TKJElectronics/BalancingRobot/3D Model/Rendered images/Back top left.jpg

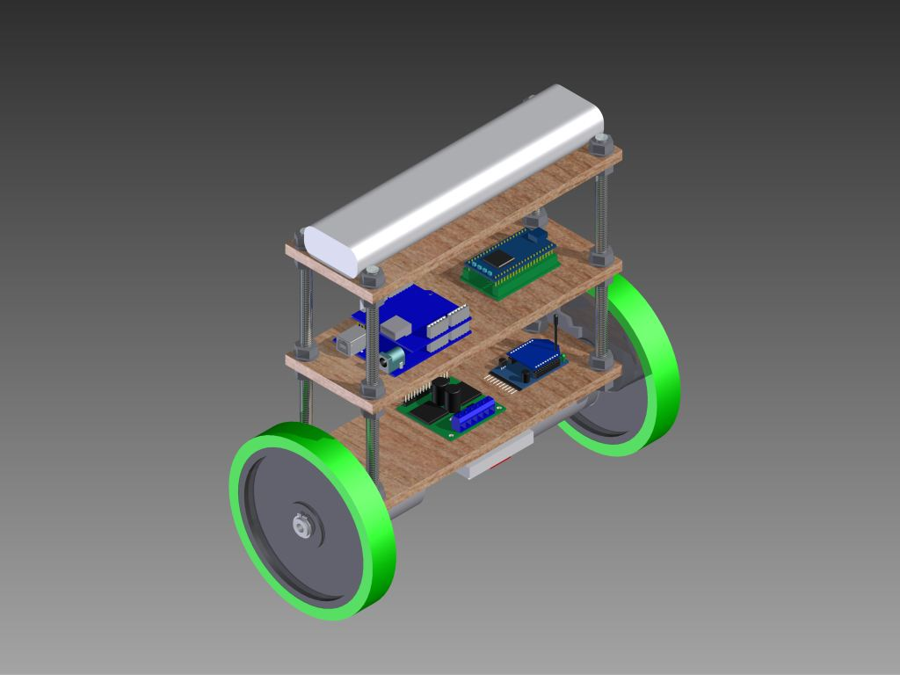
3D Model/Rendered images/Back top left.jpg
