TKJElectronics/BalancingRobot/3D Model/Rendered images/Front.jpg

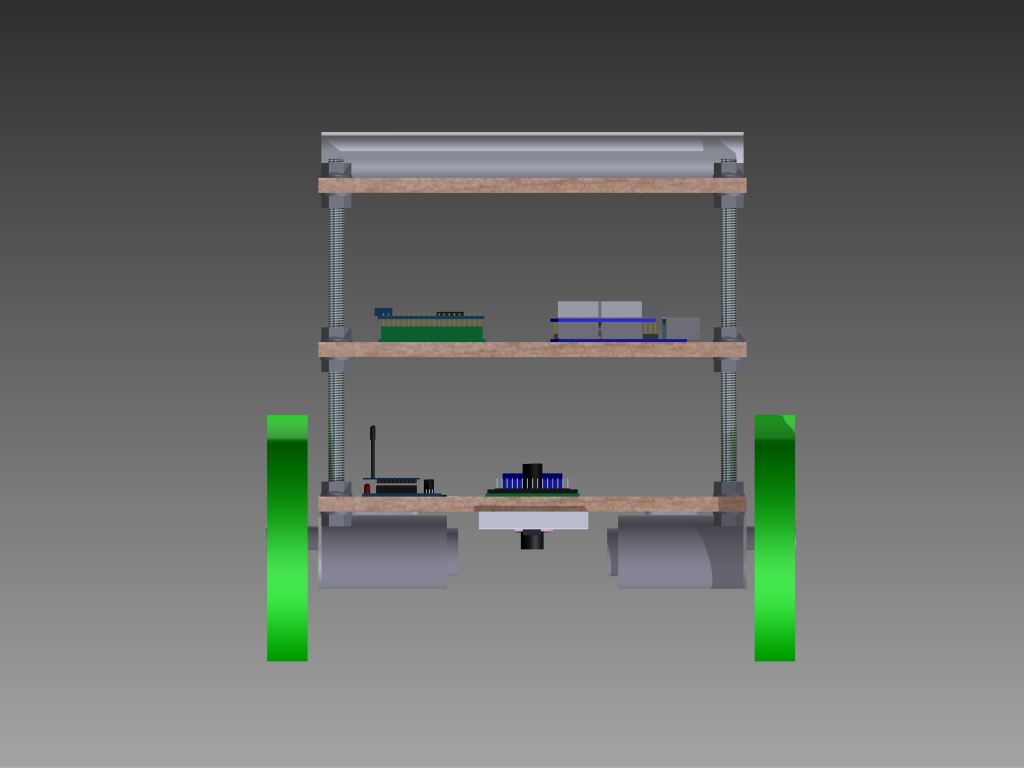
3D Model/Rendered images/Front.jpg
